JohnMacrae/Danfoss-Fridge-Control/Firmware/src/credentials.h

const char* vers = "0.1";
const char* ssid = "agboat_s";
const char* password = "jram7757";
const char* host = "fridge";
const char* MQ_client = "fridge";
const char* MQ_user = "jramacrae";
const char* MQ_pass = "jram7757";
char BrokerIP[] = "192.168.199.8";
